jbeuckm/atmega_midi_x0x_heart/MIDI_x0x/DS1267/DS1267.h

/*
  Library for controlling the Dallas Semiconductor Dual Digital Pot
*/
#ifndef DS1267_h
#define DS1267_h

#include "Arduino.h"

class DS1267
{

  public:
    DS1267(int clkPin, int dqPin, int resetPin);
    void setValue(byte pot1value, byte pot2value, byte stackBit);

  private:
    int _clkPin, _dqPin, _resetPin;
    
};

#endif
